channel2007/TBoy_ZooCube/art/ZooCube/background2.png

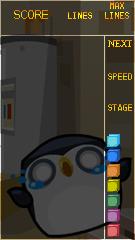
art/ZooCube/background2.png
