channel2007/TBoy_ZooCube/art/ZooCube/background3.png

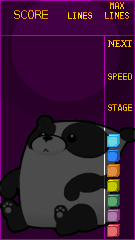
art/ZooCube/background3.png
