channel2007/TBoy_ZooCube/art/ZooCube/background5.png

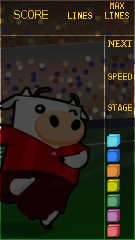
art/ZooCube/background5.png
