channel2007/TBoy_ZooCube/game/ZooCube/imgBackground1.c

#include <pgmspace.h>

// background1.png
// https://lang-ship.com/tools/image2data/

//const uint16_t background1Width = 135;
//const uint16_t background1Height = 240;

// RGB565 Dump(little endian)
const unsigned short background1[32400] PROGMEM = {
0xC442,0xC442,0xC442,0xC442,0xC442,0xC442,0xC442,0xC442,0xC442,0xC442,0xC442,0xC442,0xC442,0xC442,0xC442,0xC442,0xC442,0xC442,0xC442,0xC442,0xC442,0xC442,0xC442,0xC442,0xC442,0xC442,0xC442,0xC442,0xC442,0xC442,0xC442,0xC442,0xC442,0xC442,0xC442,0xC442,0xC442,0xC442,0xC442,0xC442,0xC442,0xC442,0xC442,0xC442,0xC442,0xC442,0xC442,0xC442,0xC442,0xC442,0xC442,0xC442,0xC442,0xC442,0xC442,0xC442,0xC442,0xC442,0xC442,0xC442,0xC442,0xC442,0xC442,0xC442,0xC442,0xC442,0xC442,0xC442,0xC442,0xC442,0xC442,0xC442,0xC442,0x8753,0x8753,0x8753,0x8753,0x8753,0x8753,0x8753,0x8753,0x8753,0x8753,0xA43A,0xC442,0xC442,0xC442,0xC442,0xC442,0xC442,0xC442,0xC442,0xC442,0xC442,0xC442,0xC442,0xC442,0xC442,0xC442,0xC442,0xC442,0xC442,0xC442,0xC442,0xC442,0xC442,0x264B,0xC442,0xC442,0xC442,0xC442,0xC442,0xC442,0xC442,0xC442,0xC442,0xC442,0xC442,0xC442,0xC442,0xC442,0xC442,0xC442,0xC442,0xC442,0xC442,0xC442,0x054B,0x8753,0x054B,0xC442,0xC442,0xC442,0xC442,0xC442,// row 0, 135 pixels
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
0x96BE,0xE639,0xE639,0x073A,0x273A,0x273A,0x273A,0x273A,0x273A,0x273A,0x073A,0x073A,0x073A,0x073A,0x073A,0x073A,0x273A,0x273A,0x273A,0x273A,0x273A,0x273A,0x273A,0x273A,0x273A,0x273A,0x273A,0x073A,0x073A,0x273A,0x273A,0x273A,0x273A,0x273A,0x273A,0x273A,0x273A,0x073A,0xA529,0x6521,0x6521,0x6521,0x6521,0x6521,0x6521,0xE631,0xE639,0xE639,0xE639,0xE639,0x073A,0x273A,0x273A,0x273A,0x273A,0x273A,0x273A,0x273A,0x273A,0x273A,0x273A,0x073A,0x073A,0x273A,0x273A,0x273A,0x273A,0x273A,0x273A,0x273A,0x273A,0x073A,0x073A,0x073A,0x073A,0x063A,0x063A,0x063A,0x063A,0x063A,0x073A,0x073A,0x073A,0x273A,0x273A,0x273A,0x273A,0xE639,0xE639,0xE639,0xE639,0xE639,0xE639,0x073A,0xE631,0x273A,0x273A,0x273A,0x273A,0x273A,0x273A,0x273A,0x273A,0x273A,0x19D7,0x273A,0xC631,0xC631,0xC631,0xA631,0xA531,0xA531,0xA631,0xC631,0xC631,0xC631,0xC631,0xC631,0xC631,0xC631,0xC631,0xC631,0xC631,0x2321,0x8108,0x8108,0x8108,0x8108,0xA110,0xA531,0xA531,0xA531,0xA531,0xA110,0x233A,// row 122, 16605 pixels
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
