channel2007/TBoy_ZooCube/game/ZooCube/imgBackground2.c

#include <pgmspace.h>

// background2.png
// https://lang-ship.com/tools/image2data/

//const uint16_t background2Width = 135;
//const uint16_t background2Height = 240;

// RGB565 Dump(little endian)
const unsigned short background2[32400] PROGMEM = {
0x10B5,0x10B5,0x10B5,0x10B5,0x10B5,0x10B5,0x10B5,0x10AD,0x10B5,0x10B5,0x10B5,0x10B5,0x10B5,0x10B5,0x10B5,0x10B5,0x10B5,0x10B5,0x10B5,0x10B5,0x10B5,0x10B5,0x10B5,0x10B5,0x10B5,0x10B5,0x10B5,0x10B5,0x10AD,0xF0AC,0xAFAC,0xAFAC,0xAFAC,0xAFAC,0xAFAC,0xAFAC,0xAFAC,0xAFAC,0xAFAC,0xAFAC,0xAFAC,0xAFAC,0xAFAC,0xAFAC,0xAFAC,0xAFAC,0xAFAC,0xAFAC,0xAFAC,0xAFAC,0xAFAC,0xAFAC,0xAFAC,0xAFAC,0xAFAC,0xAFAC,0xAFAC,0xAFAC,0xAFAC,0xAFAC,0xAFAC,0xAFAC,0xAFAC,0xAFAC,0xAFAC,0xAFAC,0xAFAC,0xAFAC,0xAFAC,0xAFAC,0xAFAC,0xAFAC,0xAFAC,0xAFAC,0xAFAC,0xAFAC,0xAFAC,0xAFAC,0xAFAC,0xAFAC,0x71BD,0x55D6,0x34D6,0x54D6,0x36D6,0x55D6,0x34D6,0x54D6,0x36D6,0x55D6,0x34D6,0x54D6,0x36D6,0x55D6,0x34D6,0x54D6,0x36D6,0x55D6,0x34D6,0x54D6,0x36D6,0x55D6,0x34D6,0x54D6,0x36D6,0x55D6,0x34D6,0x54D6,0x36D6,0x55D6,0x34D6,0x54D6,0x36D6,0x55D6,0xB1CD,0x0EBD,0x0EBD,0x0EBD,0x0EBD,0x0EBD,0x0EBD,0x0EBD,0x0EBD,0x0EBD,0x0EBD,0x0EBD,0x0EBD,0x0EBD,0x0EBD,0x0EBD,0x0EBD,0x0EBD,0x0EBD,0x0EBD,0x0EBD,// row 0, 135 pixels
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
0xD29C,0xC739,0x494A,0x0742,0xE641,0x0642,0x0642,0x0642,0x0642,0x0642,0x0642,0x0642,0x0642,0xE641,0xA631,0xE739,0xE739,0xE739,0xE739,0xE739,0xE739,0xE739,0xE739,0xE739,0xE739,0xE739,0xE739,0xE739,0xE739,0xE739,0xE739,0xE739,0xE739,0xE739,0xE739,0xE739,0xE739,0xE739,0xE739,0xE739,0xC739,0x8631,0x8631,0x8631,0x8631,0x8631,0x8631,0x8631,0x8631,0x8631,0x8631,0x8631,0x8631,0x8631,0x8631,0x8631,0x6529,0x2429,0x2329,0x2429,0x2329,0x2429,0x2329,0x2429,0x2329,0x2429,0x2329,0x2429,0x2329,0x2429,0x2329,0x2429,0x2329,0x2429,0x2329,0x4429,0x6431,0x6431,0x6431,0x6431,0x8439,0xC439,0xA539,0xA539,0xA539,0xA539,0xA539,0xA539,0xA539,0xA539,0xA539,0xA539,0xA539,0xA539,0xA539,0xA539,0xA539,0xA539,0xA539,0xA539,0xA539,0xA539,0xA539,0xA539,0xD1C5,0xC539,0x6431,0x6431,0x6431,0x6431,0x6431,0x6431,0x6431,0x6431,0x6431,0x6431,0x6431,0x6431,0x6431,0x6431,0x6431,0x6431,0x6431,0x6431,0x6431,0x6431,0x6431,0x6431,0x6431,0x6431,0x6431,0x6431,0x6431,0x6431,0xD1C5,// row 122, 16605 pixels
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
