channel2007/TBoy_ZooCube/game/ZooCube/imgBackground3.c

#include <pgmspace.h>

// background3.png
// https://lang-ship.com/tools/image2data/

//const uint16_t background3Width = 135;
//const uint16_t background3Height = 240;

// RGB565 Dump(little endian)
const unsigned short background3[32400] PROGMEM = {
0x3290,0x3290,0x3290,0x3290,0x3188,0x3080,0x3080,0x3080,0x3080,0x3080,0x3080,0x3080,0x3080,0x3080,0x3080,0x3080,0x3080,0x3080,0x3080,0x3080,0x3080,0x3080,0x3080,0x3080,0x3080,0x3080,0x3080,0x3080,0x3080,0x3080,0x3080,0x3080,0x3080,0x3080,0x3080,0x3080,0x3080,0x3080,0x3080,0x3080,0x3290,0x35A8,0x36B0,0x36B0,0x36B0,0x36B0,0x36B0,0x36B0,0x36B0,0x36B0,0x36B0,0x36B0,0x36B0,0x36B0,0x36B0,0x36B0,0x36B0,0x36B0,0x36B0,0x36B0,0x36B0,0x36B0,0x36B0,0x36B0,0x36B0,0x36B0,0x36B0,0x36B0,0x36B0,0x36B0,0x36B0,0x36B0,0x36B0,0x36B0,0x36B0,0x36B0,0x36B0,0x36B0,0x36B0,0x36B0,0x36B0,0x36B0,0x36B0,0x36B0,0x36B0,0x36B0,0x36B0,0x36B0,0x36B8,0x36B0,0x35A8,0x3290,0x3080,0x3080,0x3080,0x3080,0x3080,0x3080,0x3080,0x3080,0x3080,0x3080,0x3080,0x3080,0x3080,0x3080,0x3080,0x3080,0x3080,0x3080,0x3080,0x3080,0x3080,0x3080,0x3080,0x3080,0x3080,0x3080,0x3080,0x3080,0x3080,0x3080,0x3080,0x3290,0x3290,0x3290,0x3290,0x3290,0x3290,0x3290,0x3290,0x3290,0x3290,0x3290,0x3290,// row 0, 135 pixels
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
0x1398,0x0528,0x0528,0x0528,0x0528,0x0528,0x0528,0x0528,0x0528,0x0528,0x0528,0x0528,0x0528,0x0528,0x0528,0x0528,0x0528,0x0528,0x0528,0x0528,0x0528,0x0528,0x0528,0x0528,0x0528,0x0528,0x0528,0x0528,0x0528,0x0528,0x0528,0x0528,0x0528,0x0528,0x0528,0x2420,0x0000,0x0000,0x6108,0x8210,0x6108,0x6108,0x6108,0x6108,0x6108,0x6108,0x6108,0x6108,0x6108,0x6108,0x8210,0x4108,0x0000,0x0000,0x2000,0x2000,0x6108,0xC318,0x0421,0x6529,0xA631,0xC739,0xE739,0xE739,0x0842,0x2842,0x2842,0x2842,0x2842,0x2842,0x2842,0x2842,0x494A,0x494A,0x0842,0xE739,0xA631,0x2421,0x0421,0xA210,0xA210,0x4108,0x4108,0x4108,0x4108,0x4108,0x4108,0x2000,0x0000,0x0000,0x0000,0x0000,0x0000,0x0000,0x0000,0x2108,0x4318,0x4528,0x0528,0x0528,0x0528,0x0528,0x0528,0x0528,0x1398,0x0528,0x0420,0x0420,0x0420,0x0420,0x0420,0x0420,0x0420,0x0420,0x0420,0x0420,0x0420,0x0420,0x0420,0x0420,0x0420,0x0420,0x0420,0x0420,0x0420,0x0420,0x0420,0x0420,0x0420,0x0420,0x0420,0x0420,0x0420,0x0420,0x1398,// row 122, 16605 pixels
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
