channel2007/TBoy_ZooCube/game/ZooCube/imgBackground4.c

#include <pgmspace.h>

// background4.png
// https://lang-ship.com/tools/image2data/

//const uint16_t background4Width = 135;
//const uint16_t background4Height = 240;

// RGB565 Dump(little endian)
const unsigned short background4[32400] PROGMEM = {
0xFCA6,0xFCA6,0xFCA6,0xFCA6,0xFCA6,0xFCA6,0xFCA6,0xFCA6,0xDCA6,0xDCA6,0xFCAE,0xDCA6,0xDBA6,0xDBA6,0xFBA6,0xFBA6,0xFBA6,0xFBA6,0xFBA6,0xFBA6,0xFCA6,0xDCA6,0xFCA6,0xDCA6,0xFCA6,0xDCA6,0xDCA6,0xFCA6,0xFCA6,0xFCA6,0xFC9E,0xFC9E,0xFC9E,0xFC9E,0xFBA6,0xFBA6,0xFBA6,0xFCA6,0xDB8E,0xBA7E,0xBA7E,0xFC96,0xFCA6,0xFCA6,0xFCA6,0xDCA6,0xFBA6,0xFBA6,0xFBA6,0xFCA6,0xFCA6,0xFBA6,0xFB9E,0xFB9E,0xFCA6,0xFCA6,0xFCA6,0xFCA6,0xFCA6,0xFCA6,0xFCA6,0xFCA6,0xFC9E,0xFC9E,0xFCA6,0xDBA6,0xDBA6,0xFBA6,0xFBA6,0xFBA6,0xFBA6,0xFBA6,0xFBA6,0xFBA6,0xFBA6,0xFBA6,0xFBA6,0xFCA6,0xFCA6,0xFCA6,0xFCA6,0xFCA6,0xFCA6,0xFCA6,0xFCA6,0xFCA6,0xFCA6,0xFBA6,0xFBA6,0xFCA6,0xDCA6,0xFCA6,0x1C9F,0xDB86,0xDA7E,0xDA7E,0x1C97,0xFCA6,0xFBA6,0xFB9E,0xFBA6,0xFCA6,0xFCA6,0xFCA6,0xFBA6,0xFCA6,0xFCA6,0xDCA6,0xDCA6,0xFCA6,0xFC9E,0xFC9E,0xFC9E,0xFC9E,0xFCA6,0xFCA6,0xFCA6,0xDCA6,0xFBA6,0xFBA6,0xDCA6,0xFCA6,0xFCA6,0xDCA6,0xFCA6,0xFCA6,0x1DA7,0x1DA7,0x1CA7,0x1CA7,0x1CA7,0x1CA7,0x3C9F,0x3C9F,0x1C9F,// row 0, 135 pixels
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
